davidenascivera/BachelorThesis/CAD/Assieme/versioneM4-Estrusione-Estrusione4.SLDPRT

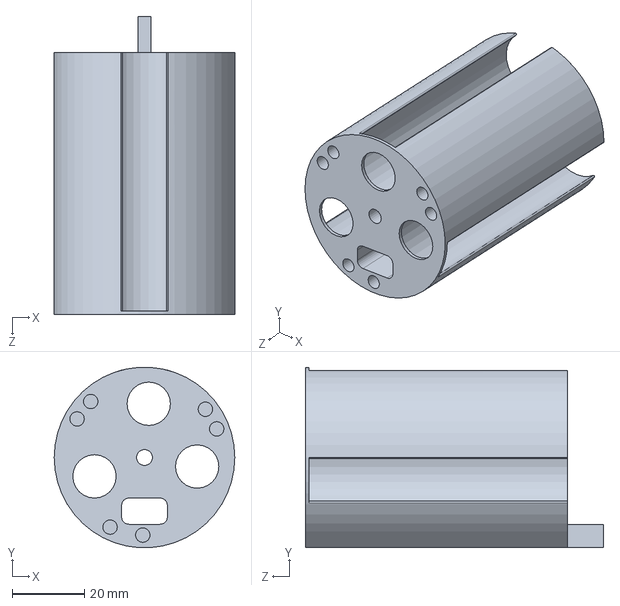
[picture p38: CAD file, 2024-09-08]
CAD/Assieme/versioneM4-Estrusione-Estrusione4.SLDPRT
50.0 x 49.9 x 82.5 mm
