davidenascivera/BachelorThesis/CAD/assieme_vecchia_versione/completo-Estrusione-Estrusione57.SLDPRT

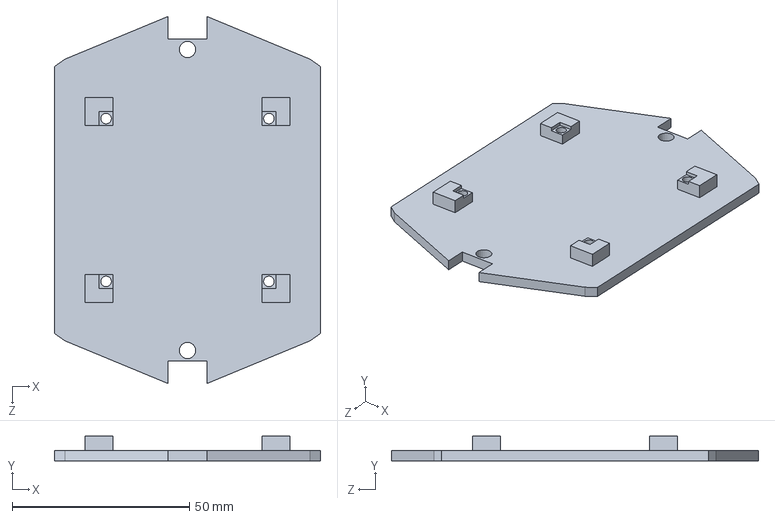
[picture p39: CAD file, 2024-09-08]
CAD/assieme_vecchia_versione/completo-Estrusione-Estrusione57.SLDPRT
75.1 x 7.00 x 103.7 mm
