davidenascivera/BachelorThesis/CAD/Assieme/versioneM4-Estrusione-Estrusione28.SLDPRT

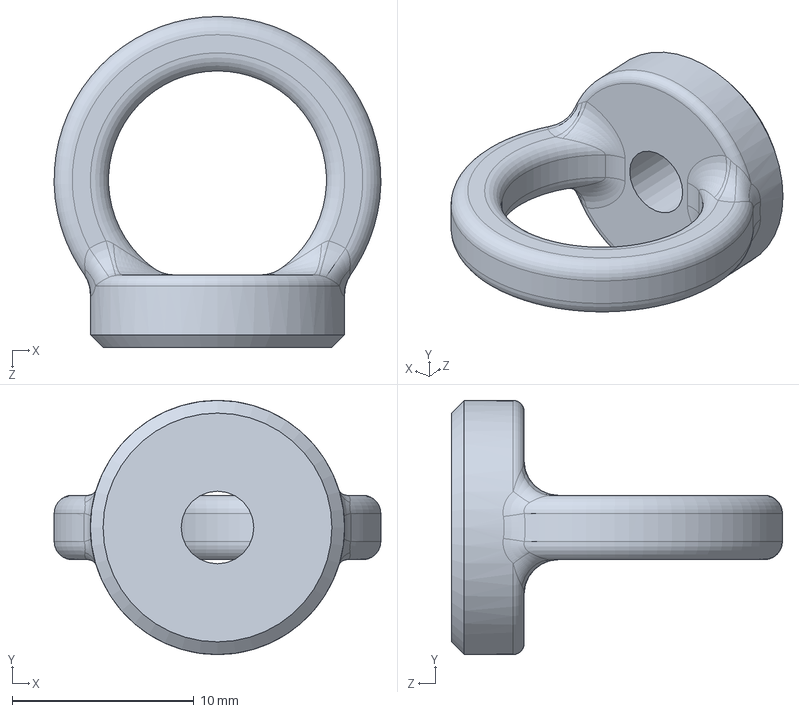
[picture p40: CAD file, 2024-09-08]
CAD/Assieme/versioneM4-Estrusione-Estrusione28.SLDPRT
18.0 x 14.0 x 18.2 mm
