davidenascivera/BachelorThesis/CAD/assieme_vecchia_versione/completo-portabatteria.SLDPRT

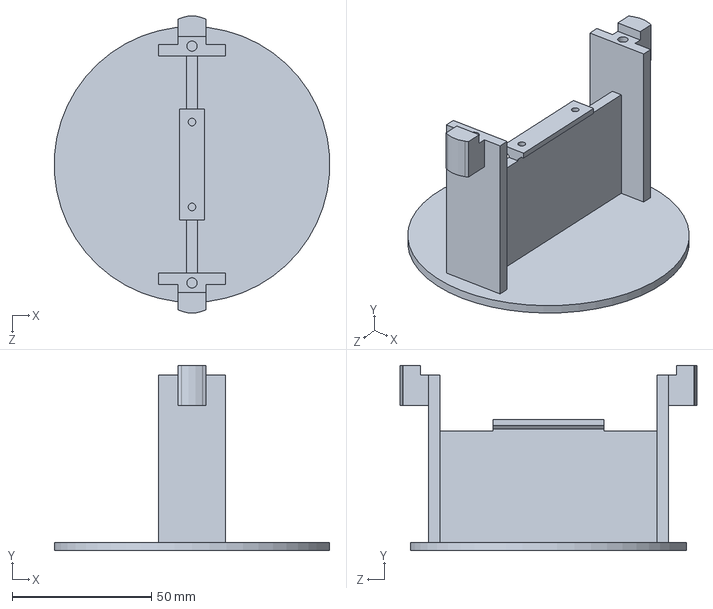
[picture p41: CAD file, 2024-09-08]
CAD/assieme_vecchia_versione/completo-portabatteria.SLDPRT
98.8 x 66.5 x 106.6 mm
