davidenascivera/BachelorThesis/CAD/Assieme/16mm Metal Pushbutton.step

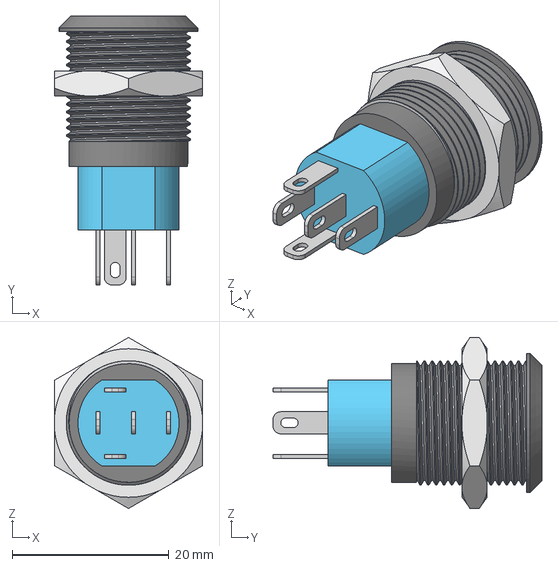
[picture p42: CAD file, 2024-09-08]
CAD/Assieme/16mm Metal Pushbutton.step
18.9 x 34.3 x 21.8 mm
