davidenascivera/BachelorThesis/CAD/Assieme/Battery spring plates.step

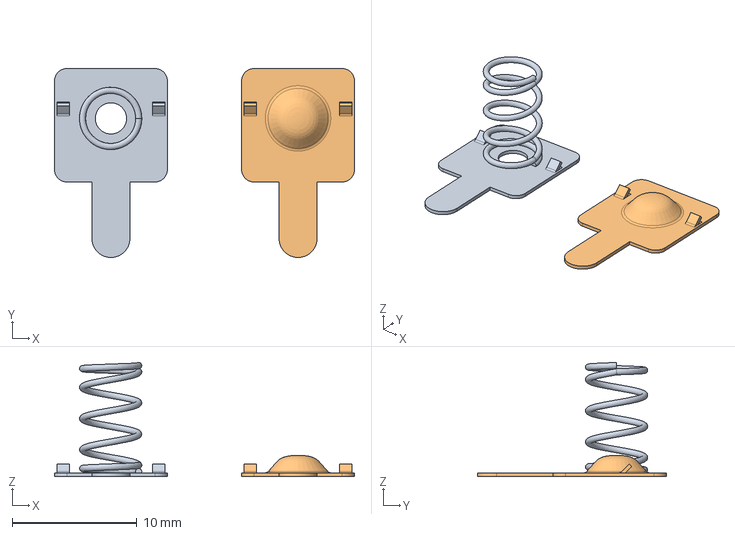
[picture p43: CAD file, 2024-09-08]
CAD/Assieme/Battery spring plates.step
24.0 x 15.1 x 9.15 mm
