davidenascivera/BachelorThesis/CAD/assieme_vecchia_versione/completo-Estrusione-Estrusione61.SLDPRT

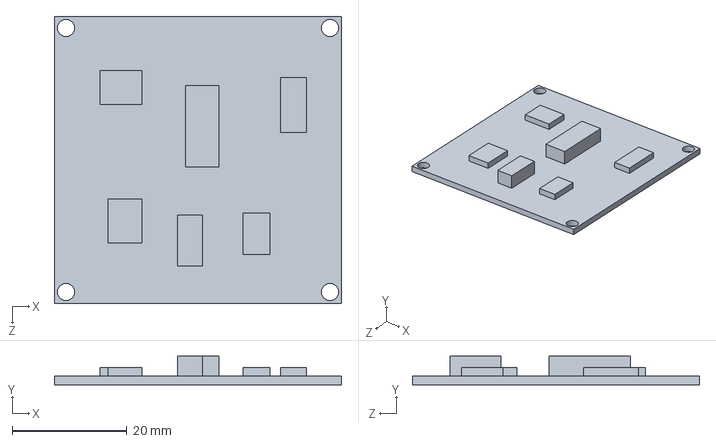
[picture p44: CAD file, 2024-09-08]
CAD/assieme_vecchia_versione/completo-Estrusione-Estrusione61.SLDPRT
50.0 x 5.00 x 50.0 mm
