davidenascivera/BachelorThesis/CAD/Assieme/plate.SLDPRT

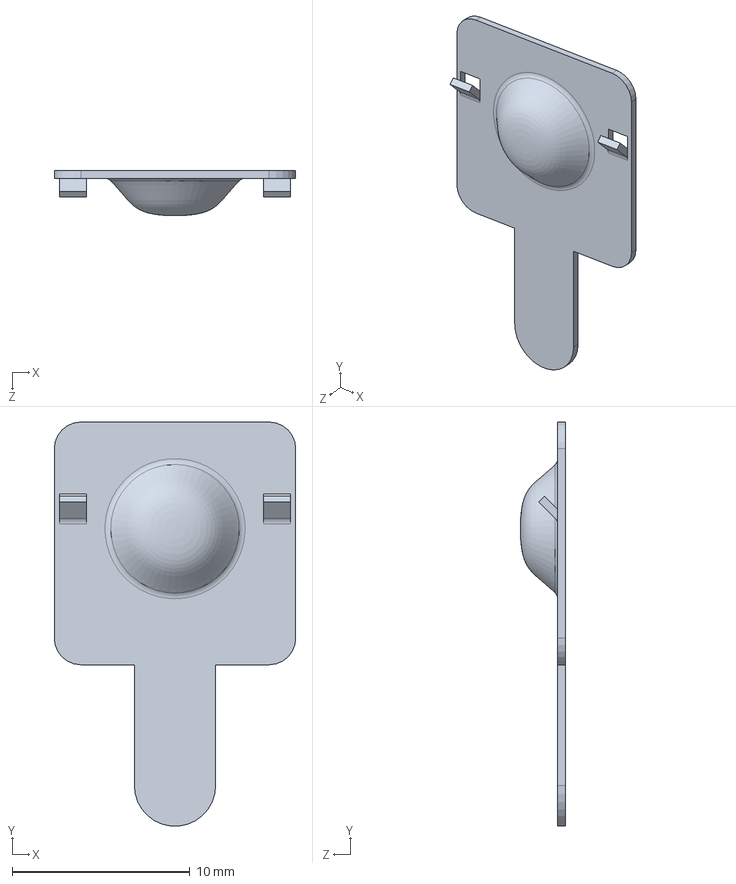
[picture p45: CAD file, 2024-09-08]
CAD/Assieme/plate.SLDPRT
13.6 x 22.7 x 2.55 mm
