davidenascivera/BachelorThesis/CAD/assieme_vecchia_versione/completo-sopra.SLDPRT

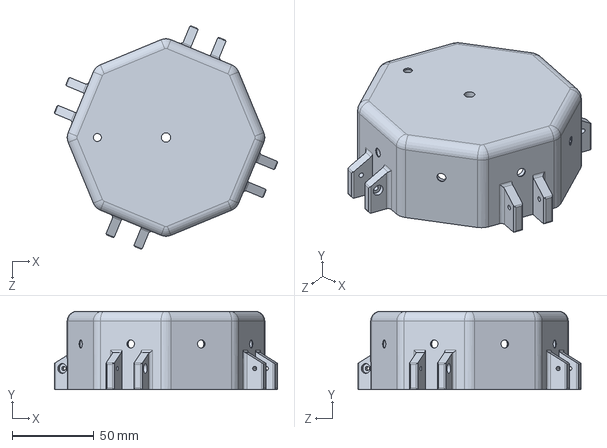
[picture p46: CAD file, 2024-09-08]
CAD/assieme_vecchia_versione/completo-sopra.SLDPRT
136.5 x 48.0 x 136.5 mm
