davidenascivera/BachelorThesis/CAD/Assieme/spring.SLDPRT

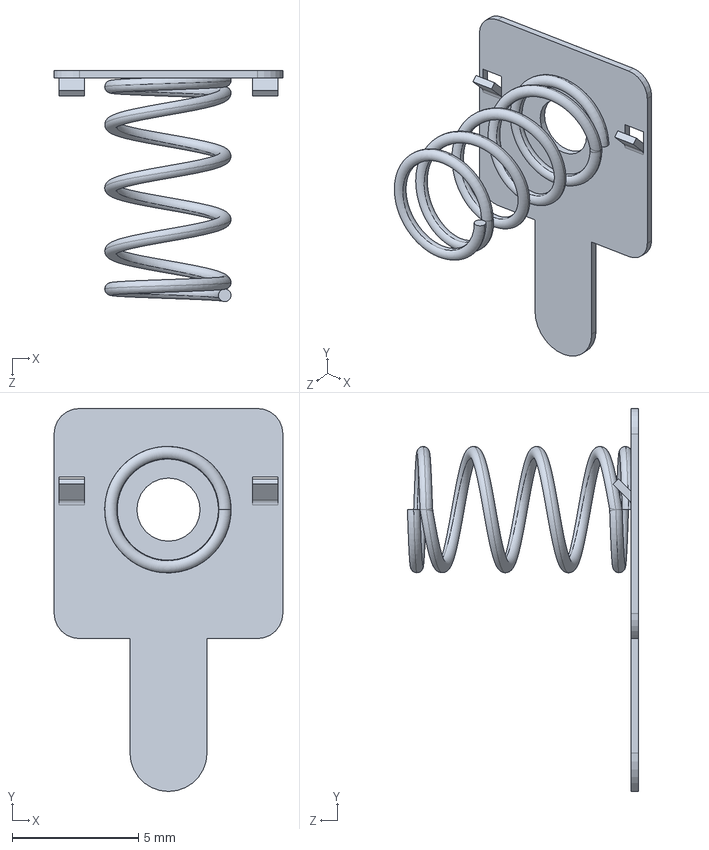
[picture p47: CAD file, 2024-09-08]
CAD/Assieme/spring.SLDPRT
9.05 x 15.1 x 9.15 mm
