davidenascivera/BachelorThesis/CAD/assieme_vecchia_versione/completo-sotto.SLDPRT

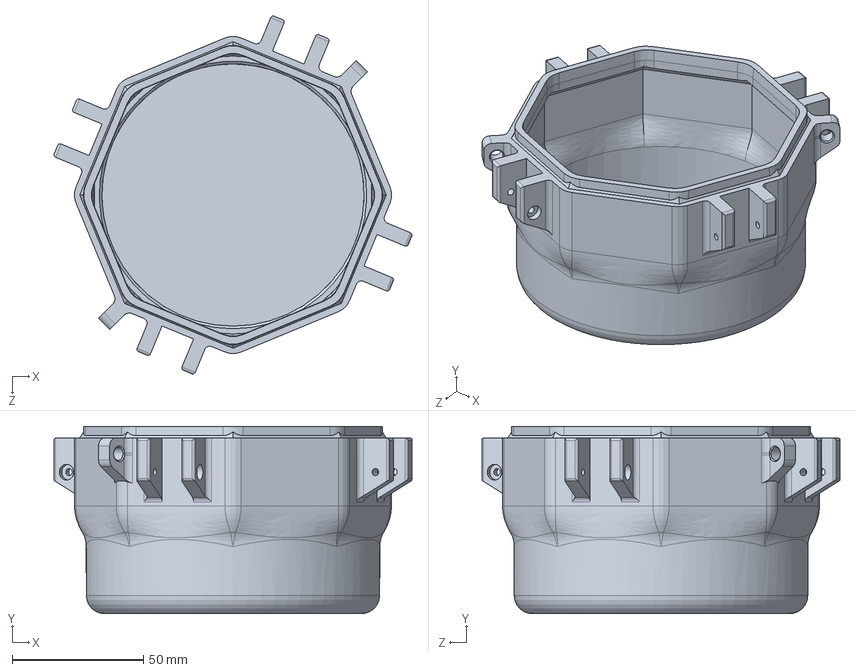
[picture p48: CAD file, 2024-09-08]
CAD/assieme_vecchia_versione/completo-sotto.SLDPRT
136.5 x 71.5 x 136.5 mm
