davidenascivera/BachelorThesis/CAD/Assieme/versioneM4-Estrusione-Estrusione21.SLDPRT

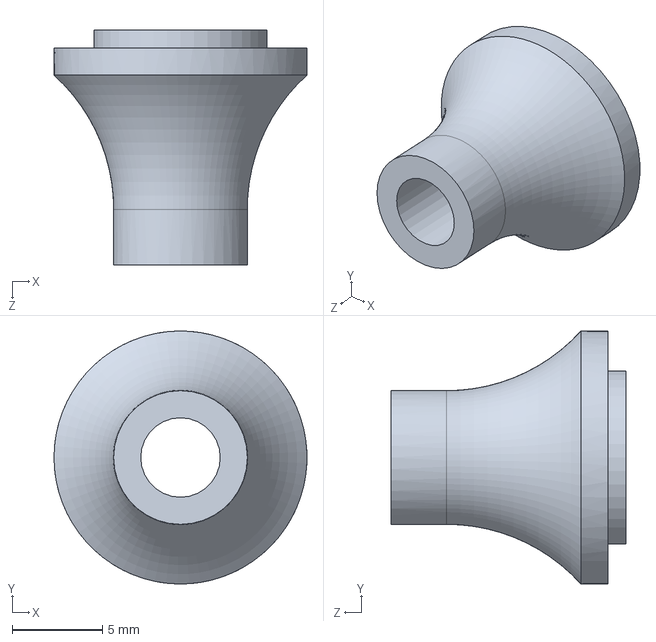
[picture p49: CAD file, 2024-09-08]
CAD/Assieme/versioneM4-Estrusione-Estrusione21.SLDPRT
14.0 x 14.0 x 13.0 mm
