davidenascivera/BachelorThesis/CAD/assieme_vecchia_versione/completo-Estrusione-Estrusione64.SLDPRT

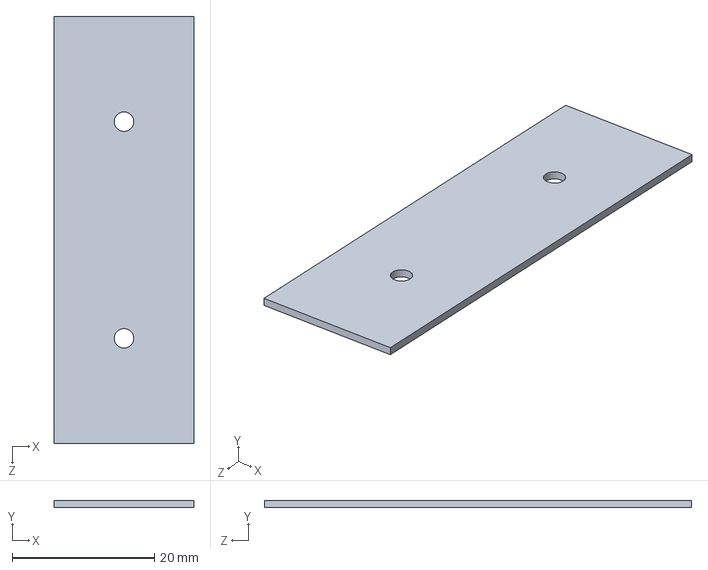
[picture p50: CAD file, 2024-09-08]
CAD/assieme_vecchia_versione/completo-Estrusione-Estrusione64.SLDPRT
19.7 x 1.00 x 60.1 mm
