davidenascivera/BachelorThesis/CAD/Assieme/usbC.SLDPRT

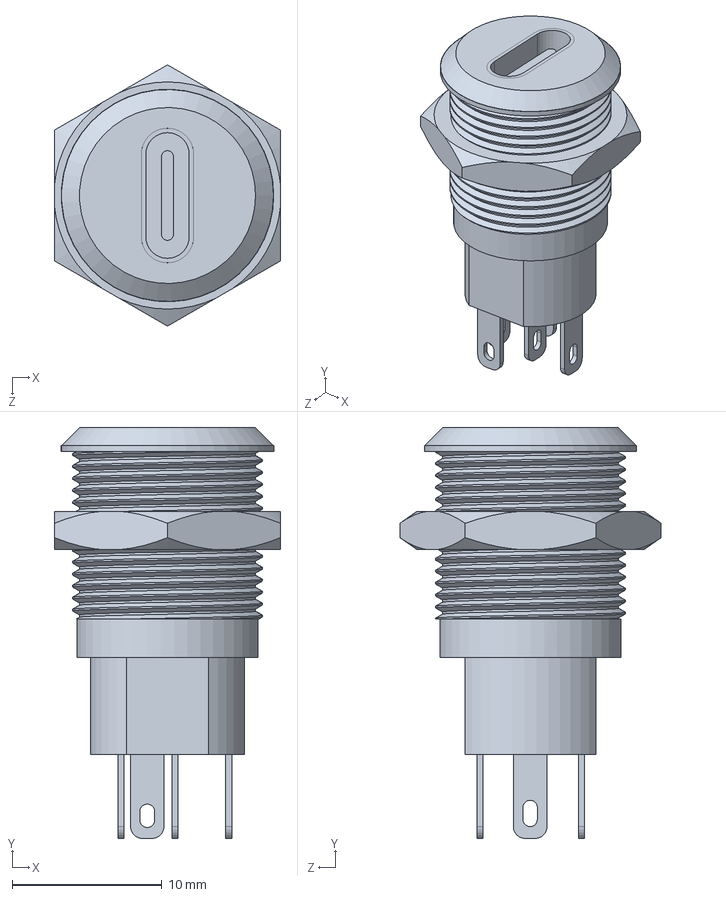
[picture p51: CAD file, 2024-09-08]
CAD/Assieme/usbC.SLDPRT
15.1 x 27.5 x 17.5 mm
