davidenascivera/BachelorThesis/CAD/assieme_vecchia_versione/NCR 18650B.STEP

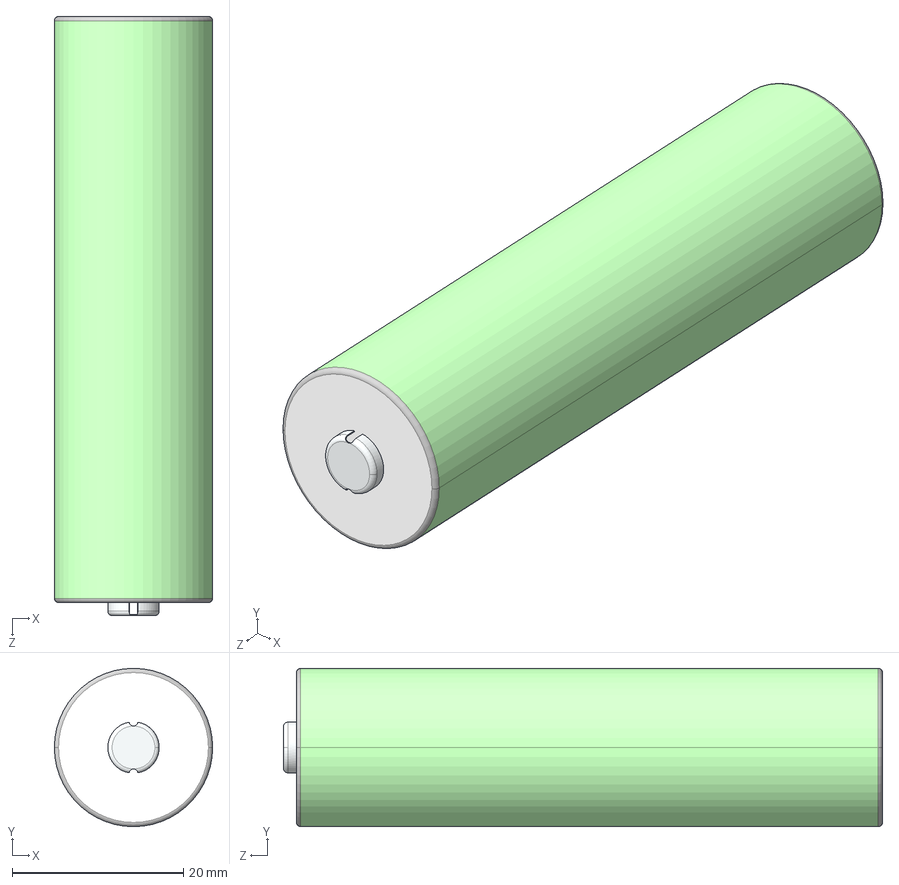
[picture p52: CAD file, 2024-09-08]
CAD/assieme_vecchia_versione/NCR 18650B.STEP
18.5 x 18.5 x 70.0 mm
