davidenascivera/BachelorThesis/CAD/Assieme/versioneM4-Estrusione-Estrusione10.SLDPRT

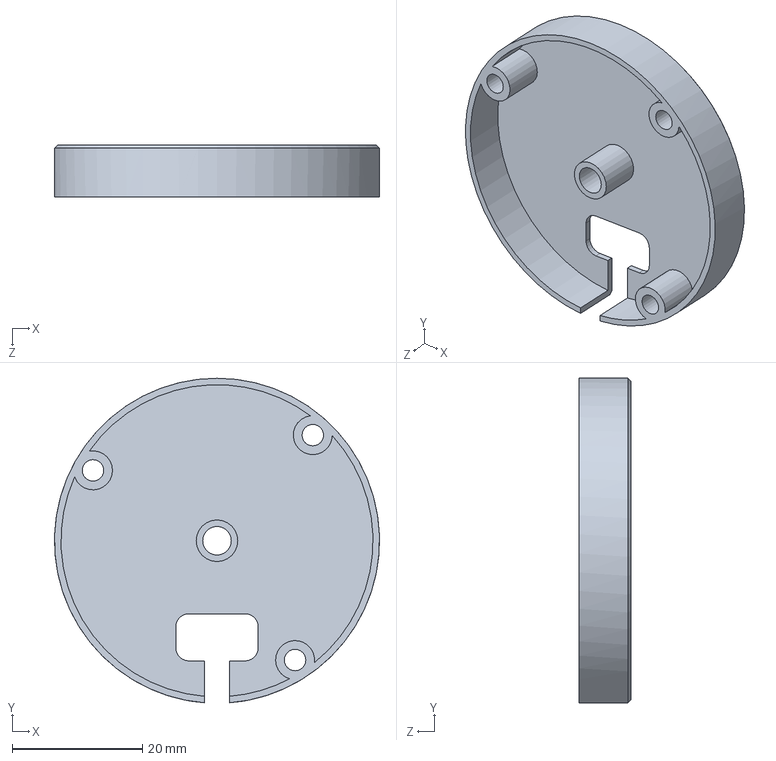
[picture p53: CAD file, 2024-09-08]
CAD/Assieme/versioneM4-Estrusione-Estrusione10.SLDPRT
50.0 x 49.9 x 8.00 mm
