davidenascivera/BachelorThesis/CAD/assieme_vecchia_versione/completo-Estrusione-Estrusione661.SLDPRT

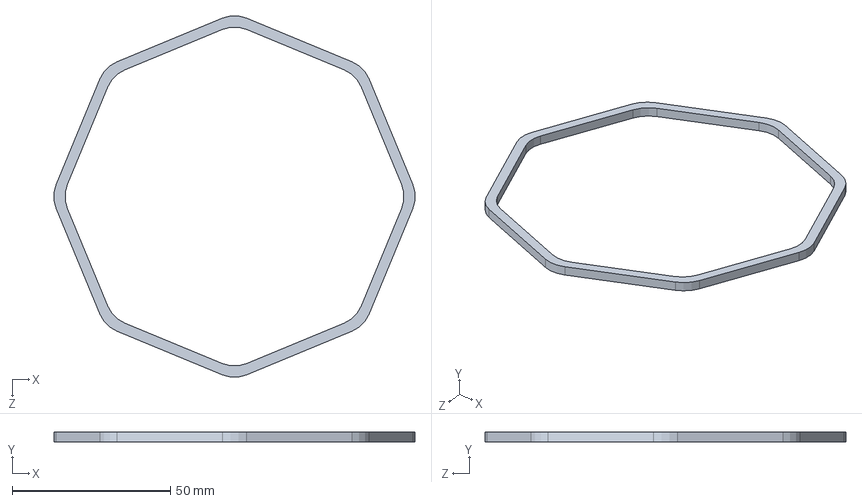
[picture p54: CAD file, 2024-09-08]
CAD/assieme_vecchia_versione/completo-Estrusione-Estrusione661.SLDPRT
114.0 x 3.00 x 114.0 mm
