davidenascivera/BachelorThesis/CAD/Assieme/pulsante.SLDPRT

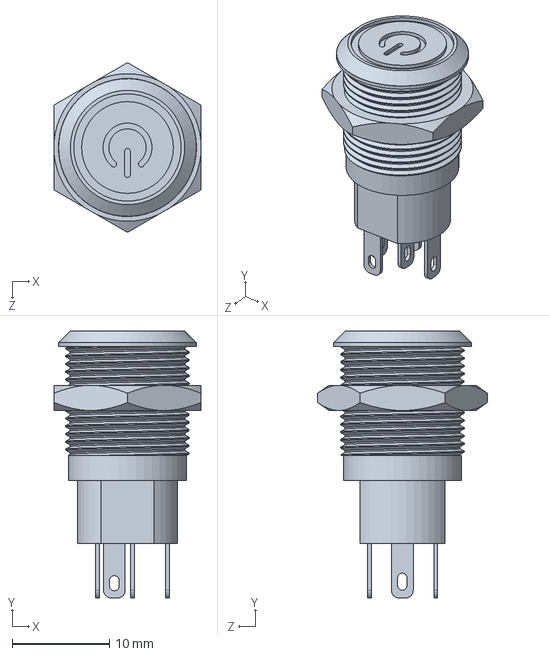
[picture p55: CAD file, 2024-09-08]
CAD/Assieme/pulsante.SLDPRT
15.1 x 27.5 x 17.5 mm
