davidenascivera/BachelorThesis/CAD/assieme_vecchia_versione/completo.SLDPRT

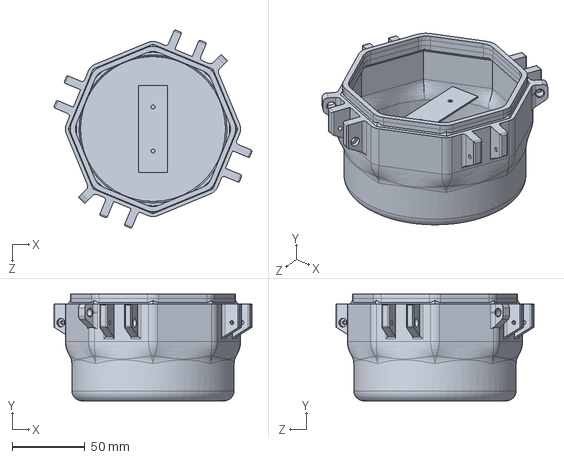
[picture p56: CAD file, 2024-09-08]
CAD/assieme_vecchia_versione/completo.SLDPRT
136.5 x 73.7 x 136.5 mm
