davidenascivera/BachelorThesis/CAD/Assieme/versioneM4-Estrusione-Estrusione25.SLDPRT

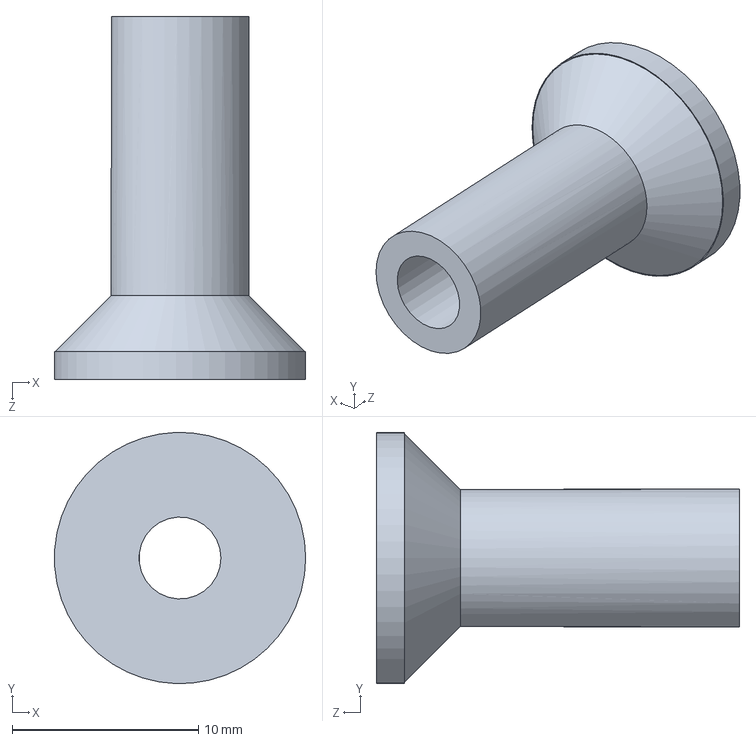
[picture p57: CAD file, 2024-09-08]
CAD/Assieme/versioneM4-Estrusione-Estrusione25.SLDPRT
13.5 x 13.5 x 19.5 mm
