davidenascivera/BachelorThesis/CAD/Assieme/versioneM4-Estrusione-Estrusione14.SLDPRT

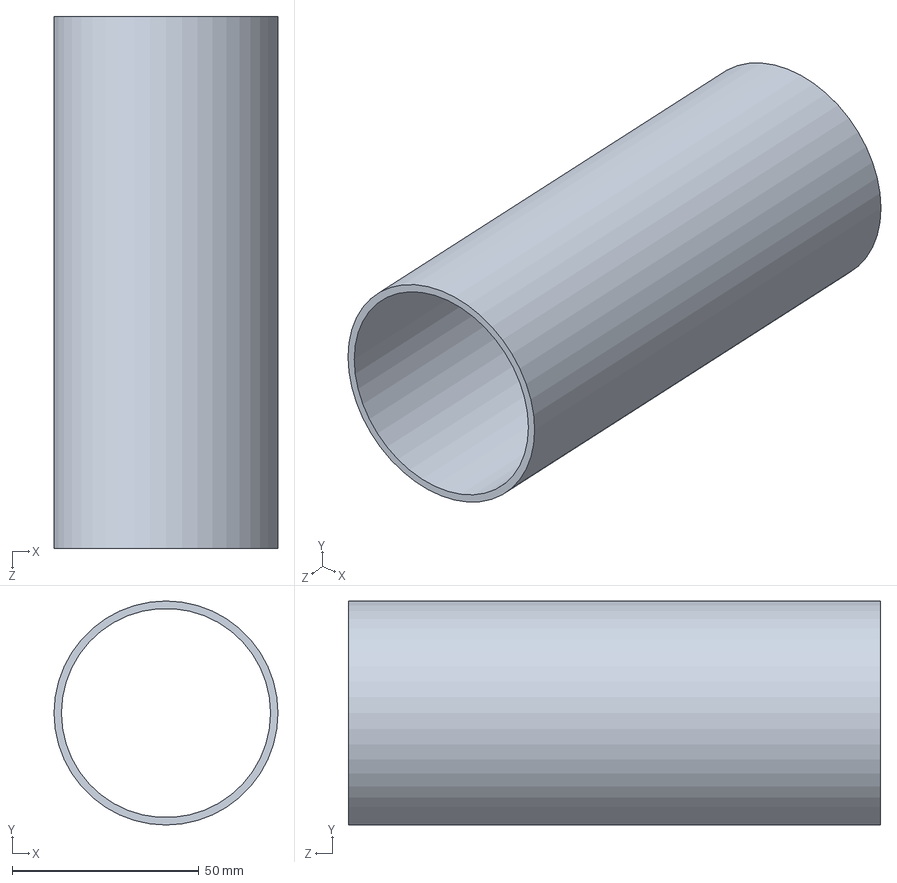
[picture p58: CAD file, 2024-09-08]
CAD/Assieme/versioneM4-Estrusione-Estrusione14.SLDPRT
60.0 x 60.0 x 142.5 mm
