davidenascivera/BachelorThesis/CAD/Assieme/User Library-JST B2B-PH-K-S.sldprt

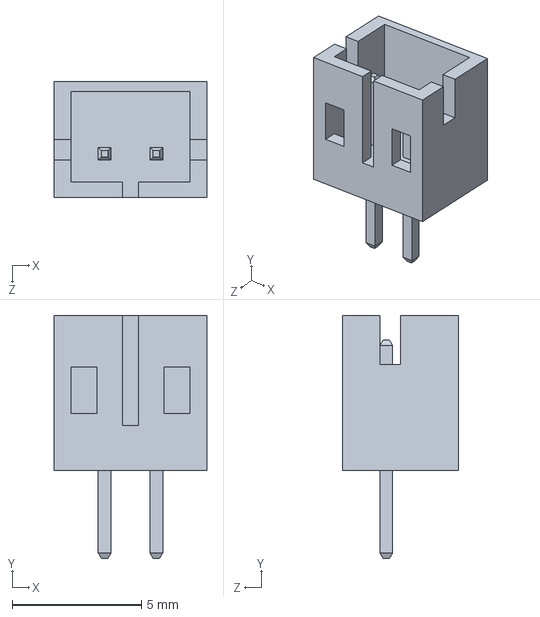
[picture p59: CAD file, 2024-09-08]
CAD/Assieme/User Library-JST B2B-PH-K-S.sldprt
5.90 x 9.40 x 4.50 mm
