davidenascivera/BachelorThesis/CAD/Assieme/versioneM4-Estrusione-Estrusione22.SLDPRT

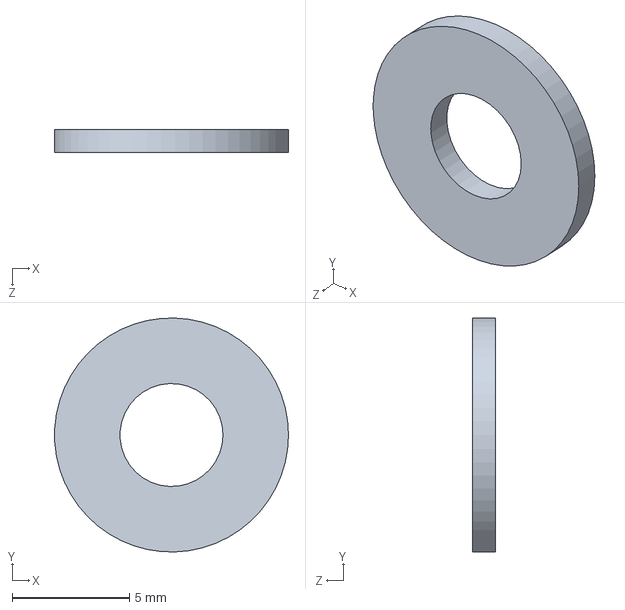
[picture p60: CAD file, 2024-09-08]
CAD/Assieme/versioneM4-Estrusione-Estrusione22.SLDPRT
10.0 x 10.00 x 1.00 mm
