davidenascivera/BachelorThesis/CAD/Assieme/BarraFilettataSemplificata.SLDPRT

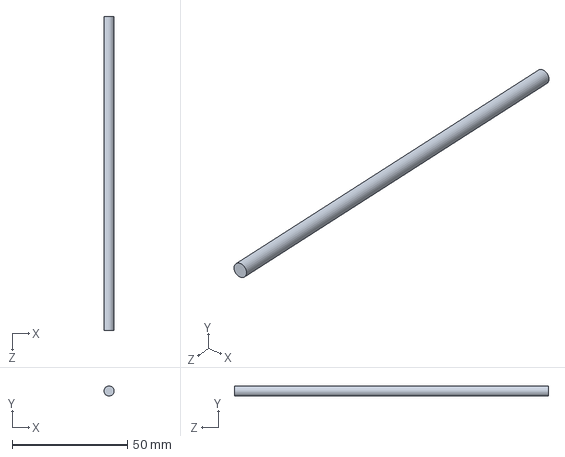
[picture p61: CAD file, 2024-09-08]
CAD/Assieme/BarraFilettataSemplificata.SLDPRT
4.39 x 4.39 x 136.0 mm
